MartinBraquet/master-thesis-UCLouvain/Thesis source code/img/196hvc-12.pdf

0

1

2

3

4

5

6

-1500

-1000

-500

0

500

1000

1500

0 | 2 | 4 | 6 | 8 | 10 | 12 | 14 | 16 | 18 | 20
| | | | | t (min)

Voltage (V)

Current (mA)

Charge cc 300 mA / 5.6 V and discharge 1 A / 3.2 V

Voltage

Current
