MartinBraquet/master-thesis-UCLouvain/Thesis source code/img/boost_efficiency.pdf

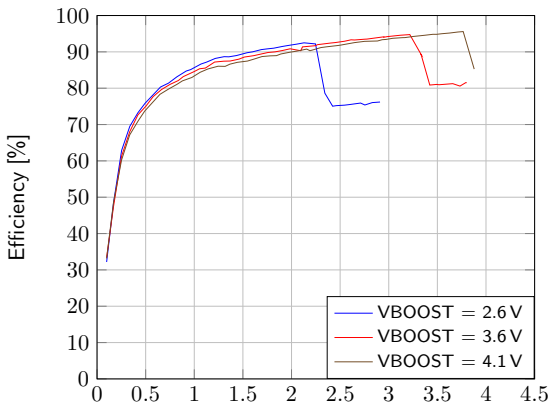
[picture p6: figure]
Efficiency [%]; VBOOST = 2.6 V VBOOST = 3.6 V; VBOOST = 4.1 V

VSRC [V] (ISRC = 10 mA)
