MartinBraquet/master-thesis-UCLouvain/Audio processing/greattit_full-1.png

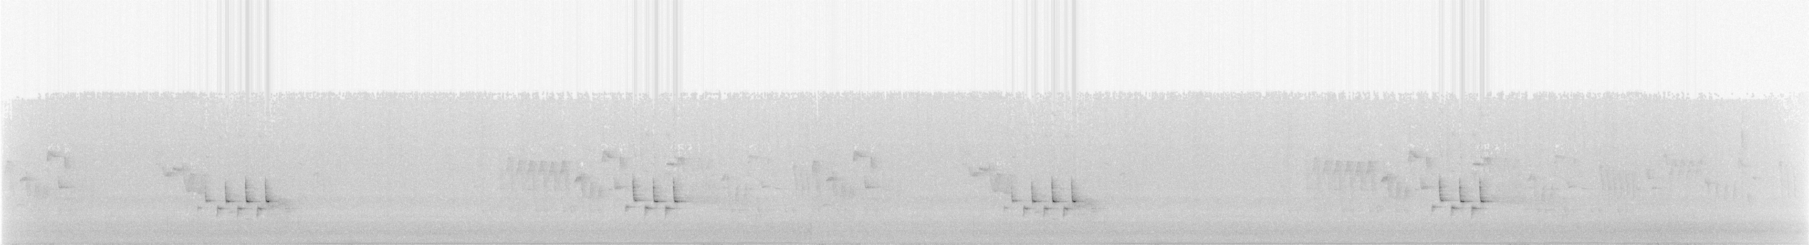
Audio processing/greattit_full-1.png
