MartinBraquet/master-thesis-UCLouvain/Thesis source code/img/sensing_PMU_schematic.pdf

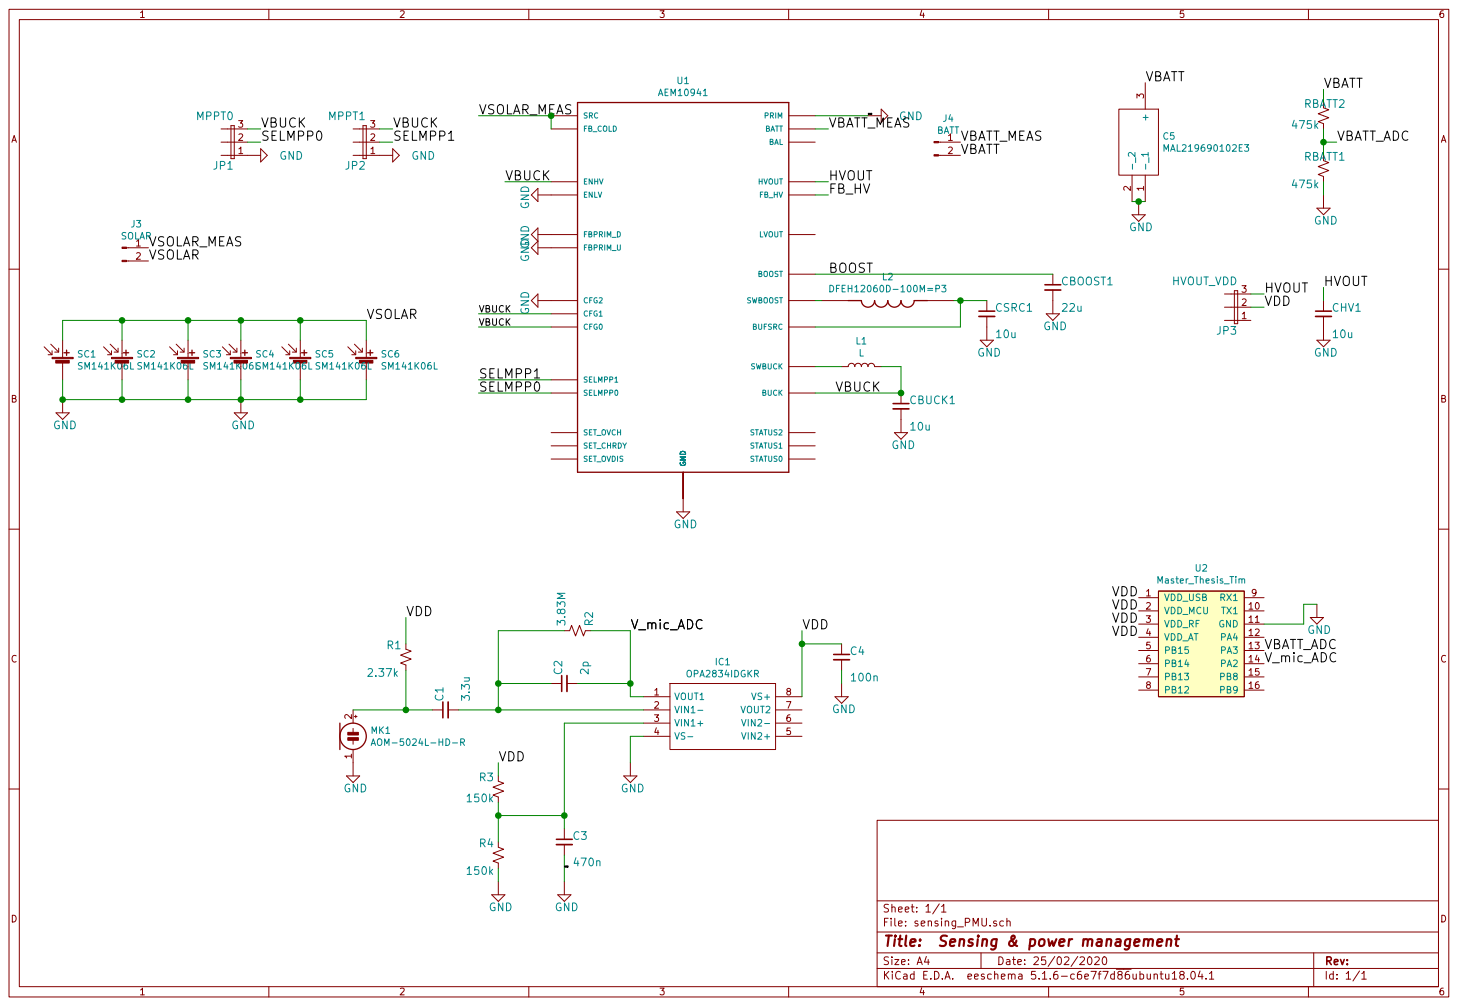
[picture p19: page 1]

FB_HV HVOUT BAL BATT PRIM

Id: 1/1 Title: Sensing & power management
