MartinBraquet/master-thesis-UCLouvain/Thesis source code/img/sensing_PMU_layout.pdf

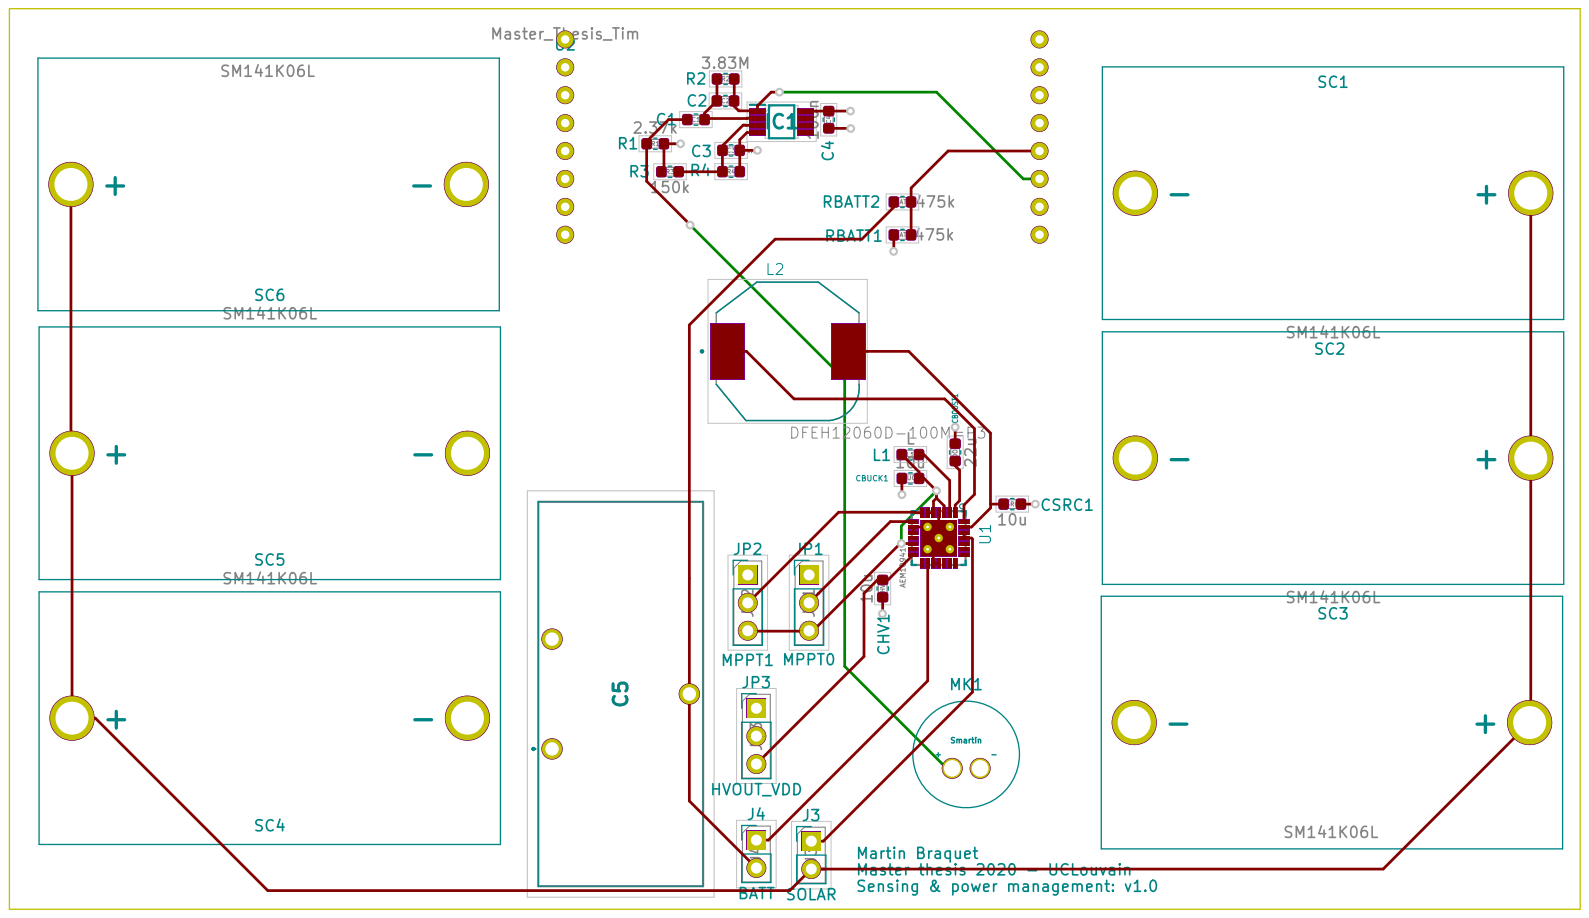
[picture p21: page 1]
