MartinBraquet/master-thesis-UCLouvain/PCB/KiCad/MCU_TX/Order/Schematic.pdf

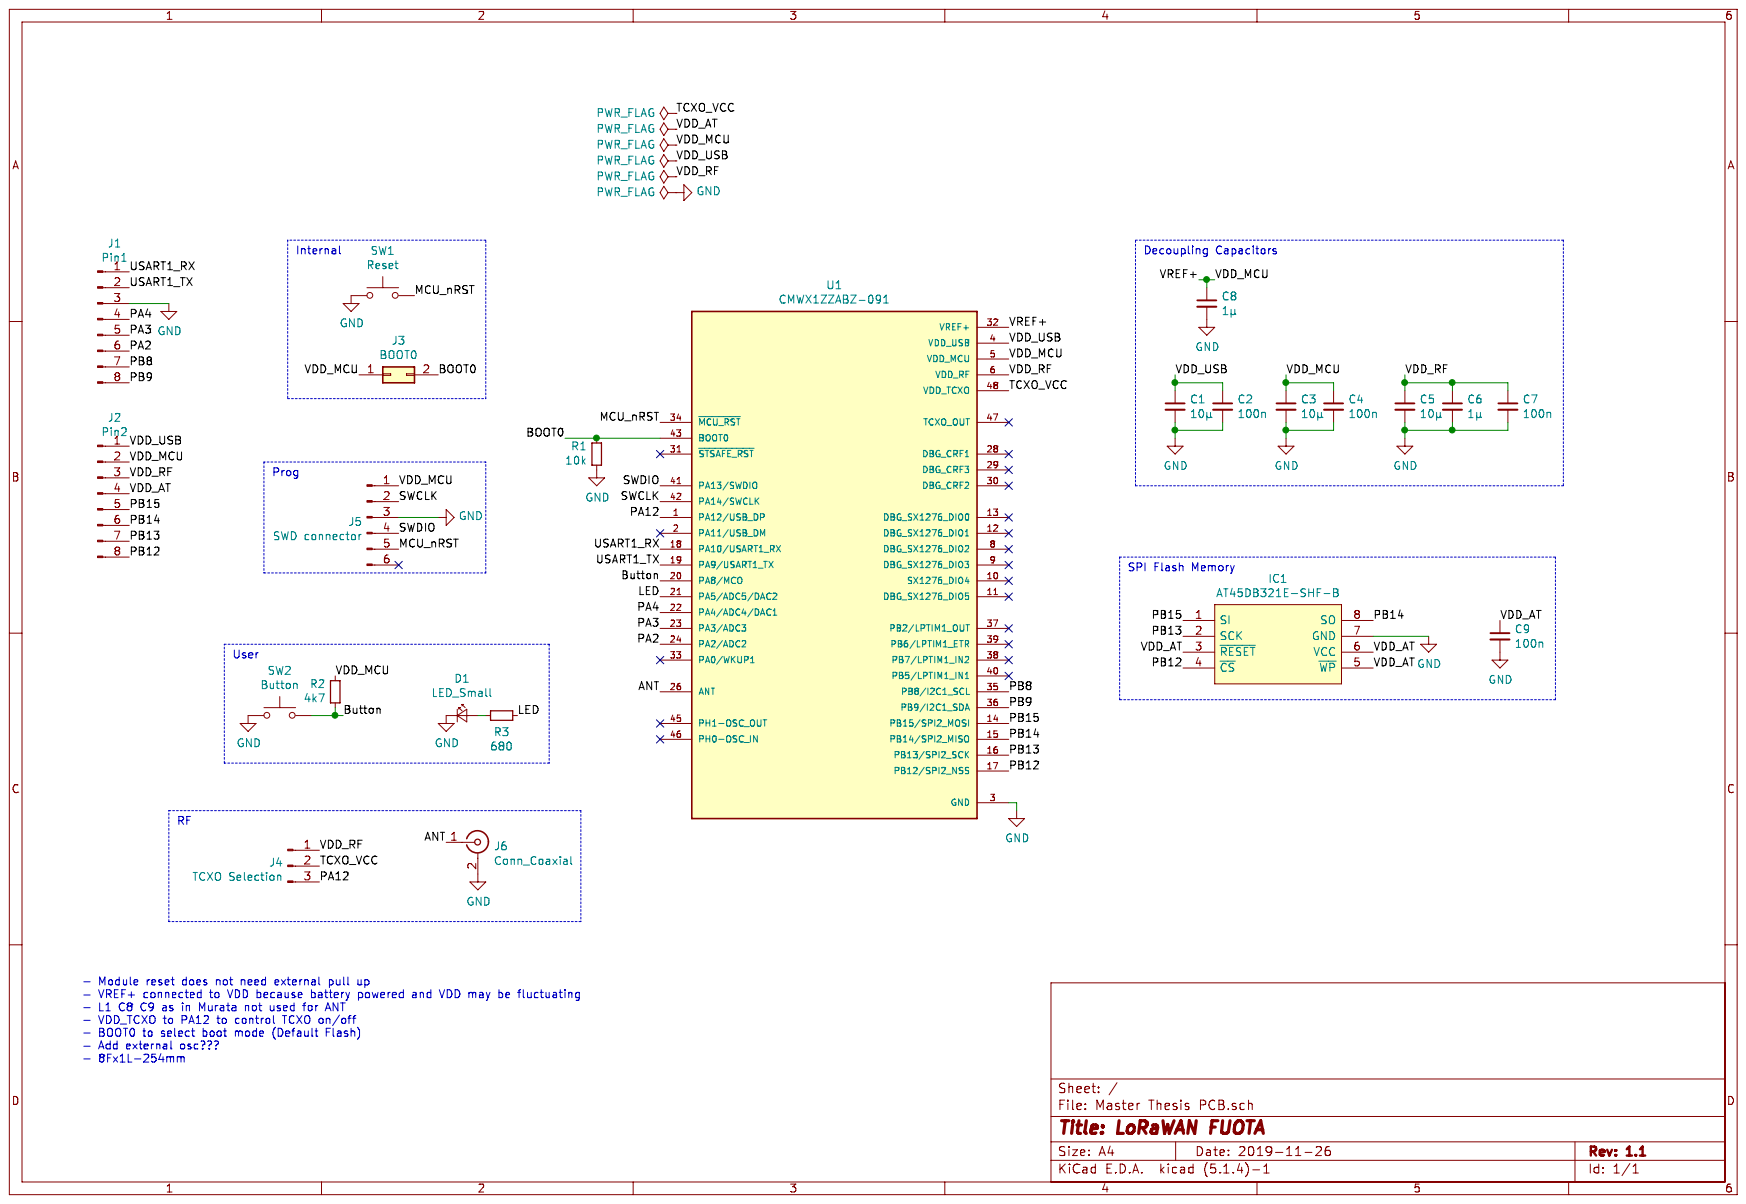
[picture p22: page 1]
