MartinBraquet/master-thesis-UCLouvain/Microphone/micelectret1_test1.asc

R1: res; 2.2k
U1: micelectret1; frec=3000 dBSPL=94 Sens=-24
V1: battery; 3
Named nets: 0, out, V+
.op
.tran 0 10m 0 1u
.options plotwinsize=0
