MartinBraquet/master-thesis-UCLouvain/Microphone/microphone test IV.asc

U2: micelectret1; frec=1000   dBSPL=60  Sens=-24
VCC: voltage_us; 3.6
Named nets: VCC, 0
Electret microphone model:
Imax = 0.5 mA
V = 2 V
S = -24 dB
.dc VCC 0 5 0.01
.inc TLV9001.sub
