MartinBraquet/master-thesis-UCLouvain/Microphone/microphone_report.asc

C1: cap; 6.68u
C2: cap; 16.7p
C3: cap; 64n
R1: res; 4.76k
R2: res; 71.4k
R3: res; 1Meg
R4: res; 1Meg
U1: OPA2834
U2: micelectret1; frec=1000   dBSPL=88  Sens=-24
Named nets: VCC, 0, Vout
Electret microphone model
