MartinBraquet/master-thesis-UCLouvain/Microphone/microphone_tests.asc

A: voltage_us; 0
C1: cap; 1µ
C7: cap; 100p
J1: njfet
J2: njfet
R1: res; 1k
R2: res; 1G
V1: voltage_us; 4
V2: signal_square; SINE(1 10m 1k)
V4: voltage_us; 1
Named nets: 0, VCC
.tran 10m
;dc A 0.4 5 0.02
