MartinBraquet/master-thesis-UCLouvain/Microphone/microphone_op_amp.asc

U1: OPA2834
VCC1: voltage_us; 1.25; AC 1 0
VCC: voltage_us; 2.5
Named nets: 0, VCC, Vout
;tran 0 50m
.ac dec 10 1 100G
.inc OPA2834.sub
