MartinBraquet/master-thesis-UCLouvain/Microphone/micelectret1_DC_sweep.asc

A: voltage_us; 0
U1: micelectret1; frec=1000 dBSPL=90
Named nets: 0
.dc A 0 10 0.01
