MartinBraquet/master-thesis-UCLouvain/Microphone/microphone.asc

C5: cap; 3.34µ
C6: cap; 100p
C7: cap; 2.09p
C8: cap; 424n
C9: cap; 100n
R5: res; 2.38k
R6: res; 3.8Meg
R7: res; 150k
R8: res; 150k
U2: micelectret1; frec=1000   dBSPL=88  Sens=-24
U3: OPA2834
VCC: voltage_us; 2.5
Named nets: 0, VCC, Vout
Electret microphone model:
Imax = 0.21 mA
V = 2 V
S = -24 dB
;tran 0 50m
.ac dec 10 1 100K
.inc OPA2834.sub
