MartinBraquet/master-thesis-UCLouvain/Microphone/microphone_noise.asc

C1: cap; 100p
C5: cap; 3.34µ
C7: cap; 2.09p
C8: cap; 424n
C9: cap; 100p
I1: current_us; 1
R5: res; 2.38k
R6: res; 3.8Meg
R7: res; 150k
R8: res; 150k
U1: OPA2834
VCC: voltage_us; 2.5
Named nets: VCC, 0, Vout
.noise V(Vout) I1 dec 100 1p 100G
;ac dec 10 1 100K
.inc OPA2834.sub
