MartinBraquet/master-thesis-UCLouvain/Power management/power management.asc

C2: cap; 16.7p
C6: cap; 100p
R2: res; 71.4k
R3: res; 1Meg
R4: res; 1Meg
VCC: voltage_us; 3.0
Named nets: VCC, 0
.tran 0 50m
;ac dec 10 1 100K
.inc OPA2834.sub
